abhishekpratapa/Comfort-Sensor/images/bottom_board_PCB.png

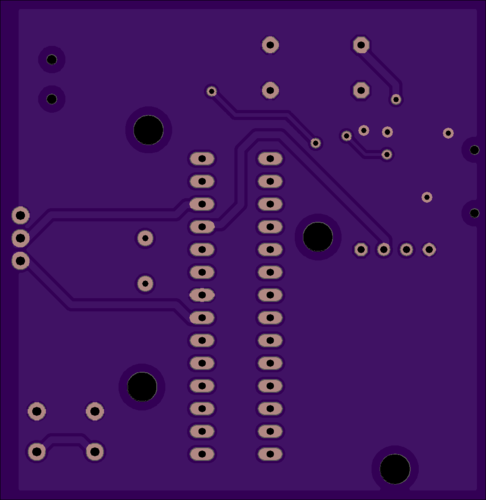
images/bottom_board_PCB.png
