abhishekpratapa/Comfort-Sensor/images/top_board_PCB.png

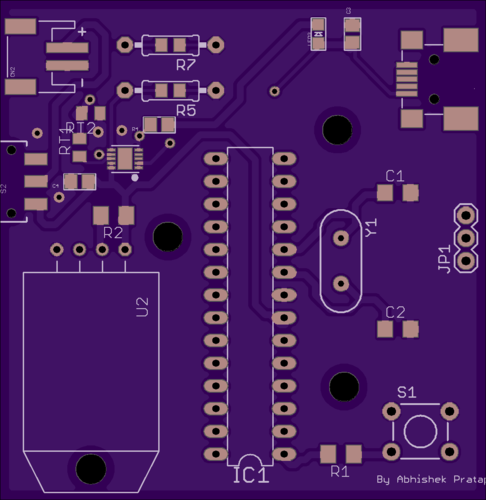
images/top_board_PCB.png
